HouseOfBeck/BeagleQ/images/beagleq-2.jpg

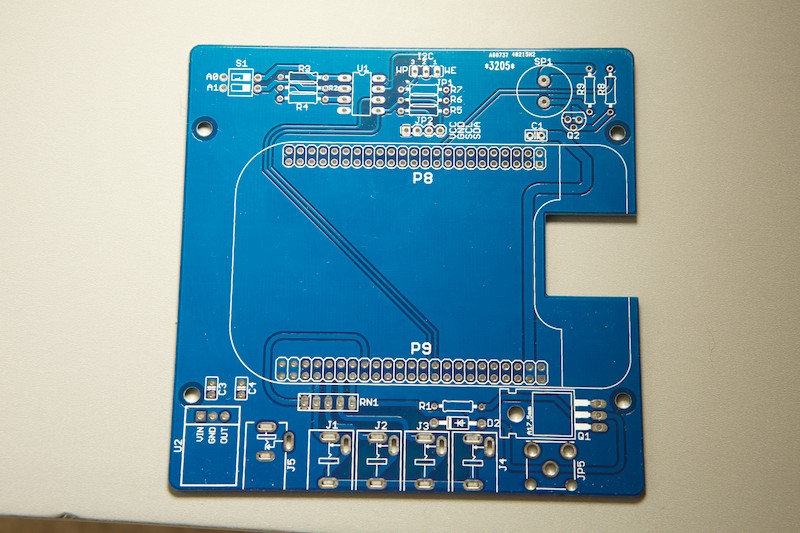
images/beagleq-2.jpg
