HouseOfBeck/BeagleQ/images/beagleq-3.jpg

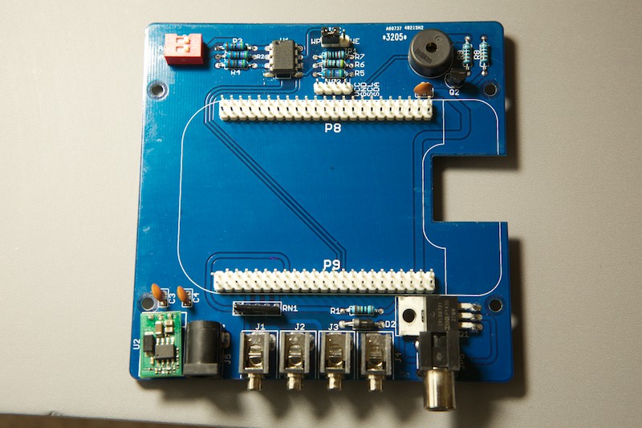
images/beagleq-3.jpg
