HouseOfBeck/BeagleQ/images/beagleq-4.jpg

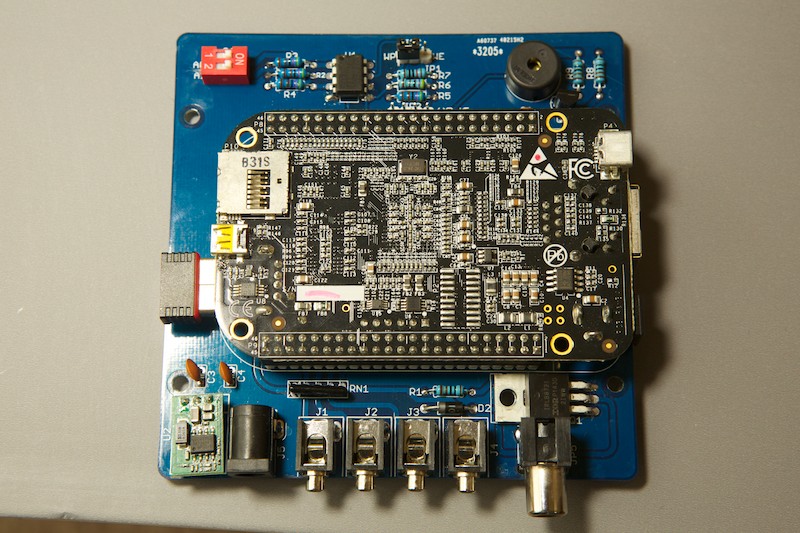
images/beagleq-4.jpg
