HouseOfBeck/BeagleQ/images/beagleq-7.jpg

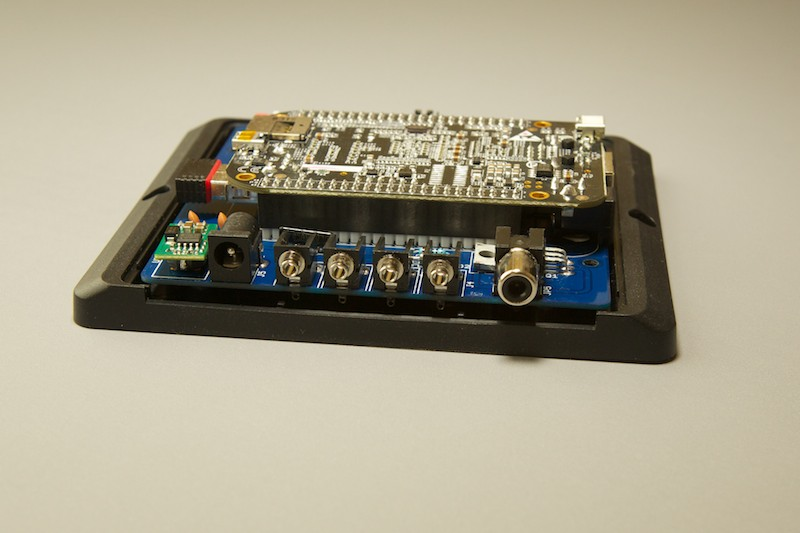
images/beagleq-7.jpg
