HouseOfBeck/BeagleQ/images/beagleq-screen-chart.png

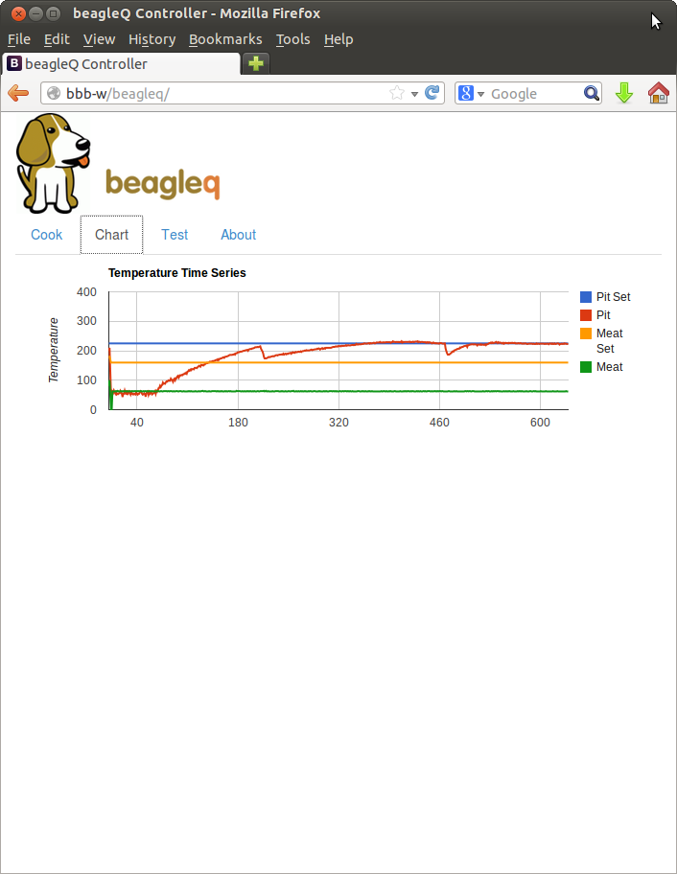
images/beagleq-screen-chart.png
